HabonRoof/PD-AuxPower-Card/Core/Inc/pd_sink.h

/*
 * pd_sink.h
 *
 *  Created on: Sep 27, 2023
 *      Author: johnson
 */

#ifndef INC_PD_SINK_H_
#define INC_PD_SINK_H_

// Power Data Object
typedef struct{

}PDO_t;

// Request Data Object
typedef struct{

}RDO_t;

// PD data structure
typedef struct{

}PD_t;

#endif /* INC_PD_SINK_H_ */
